google/mozc-devices/mozc-furikku/circuit.png

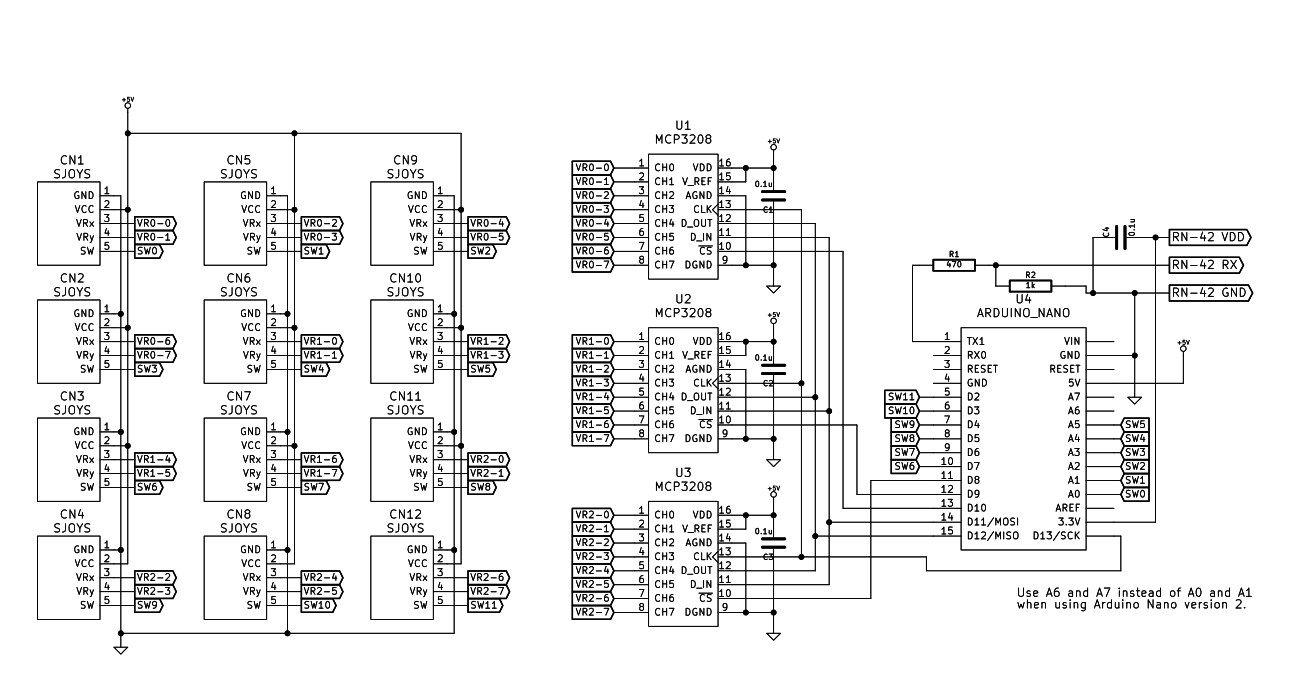
mozc-furikku/circuit.png
