google/mozc-devices/mozc-furikku/photo/device.jpg

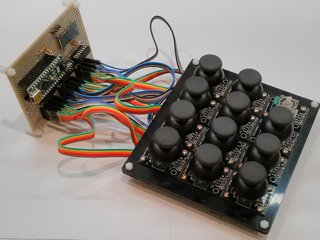
mozc-furikku/photo/device.jpg
