google/mozc-devices/mozc-furikku/photo/jsmodule.jpg

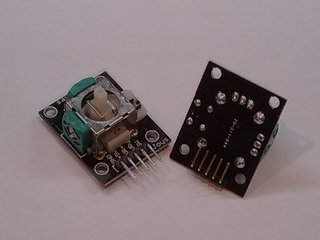
mozc-furikku/photo/jsmodule.jpg
