google/mozc-devices/mozc-furikku/photo/keyboard.jpg

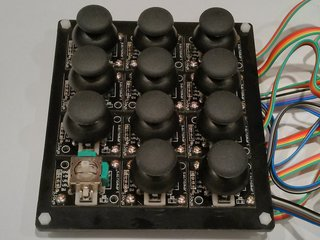
mozc-furikku/photo/keyboard.jpg
