google/mozc-devices/mozc-mageru/wireless/board/board-bottom.png

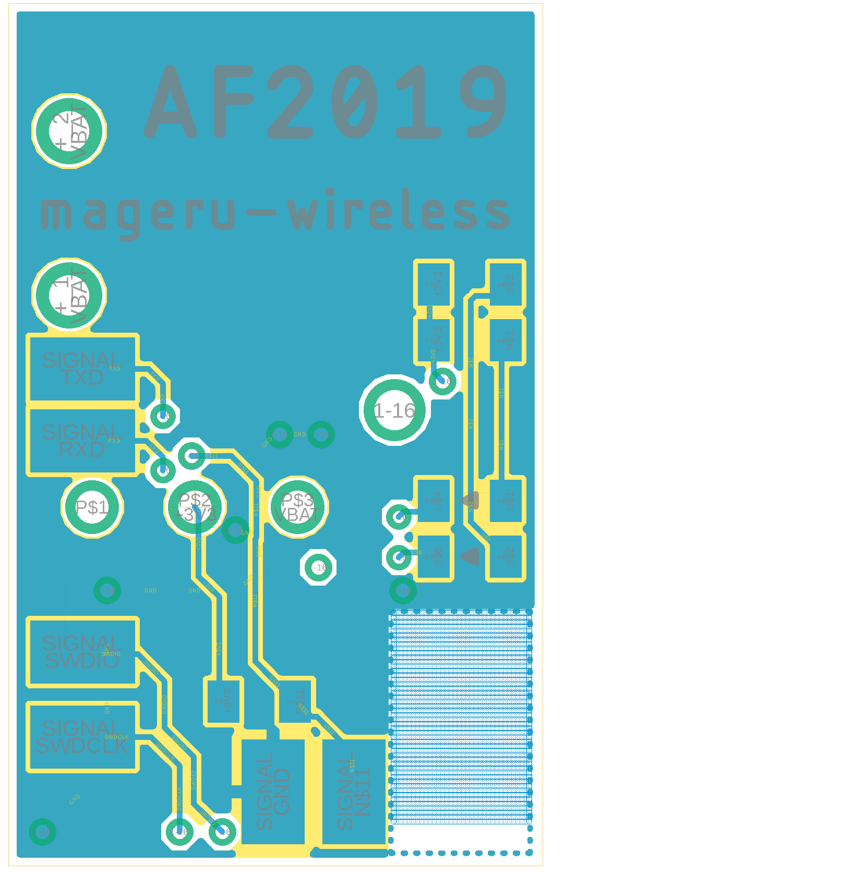
mozc-mageru/wireless/board/board-bottom.png
