google/mozc-devices/mozc-mageru/wireless/board/board-top.png

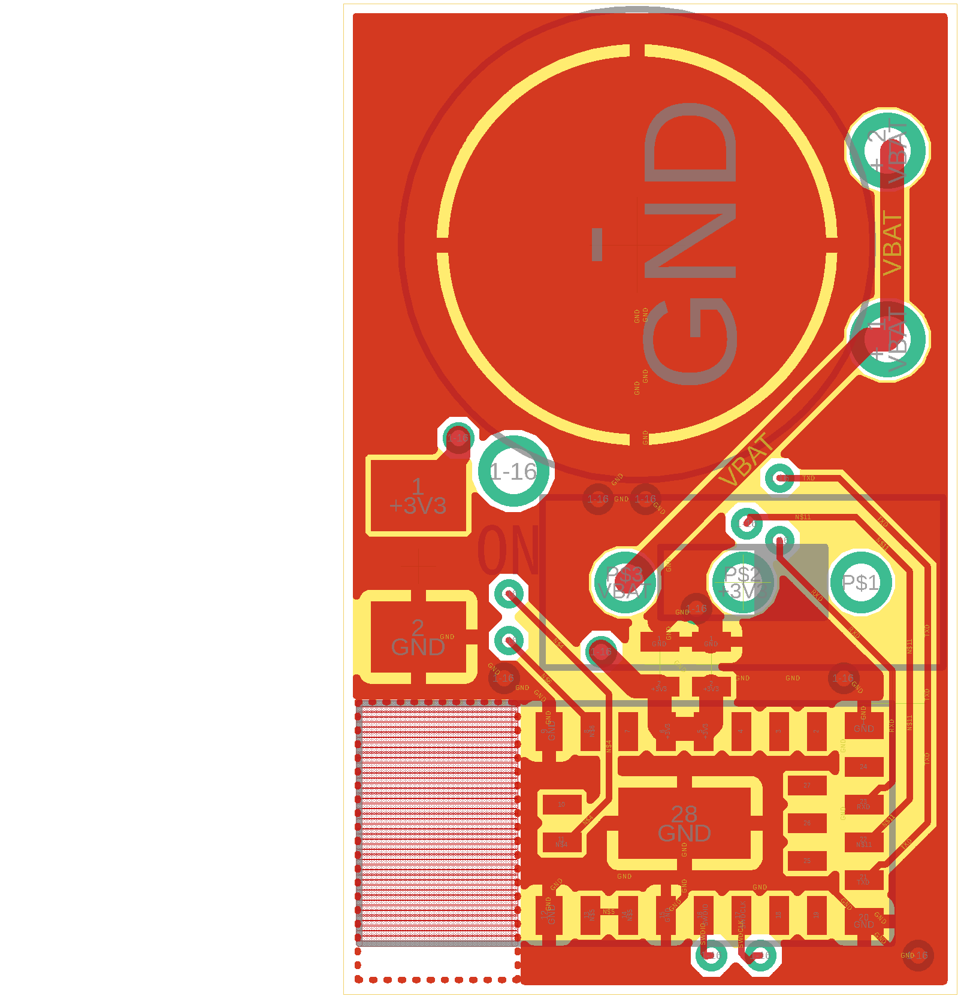
mozc-mageru/wireless/board/board-top.png
