google/mozc-devices/mozc-piropiro/circuit.png

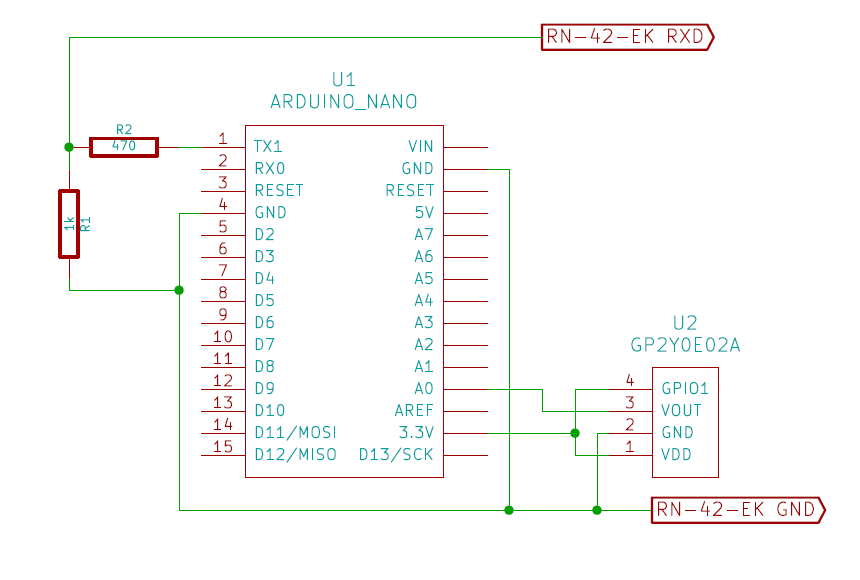
mozc-piropiro/circuit.png
