google/mozc-devices/mozc-piropiro/example.jpg

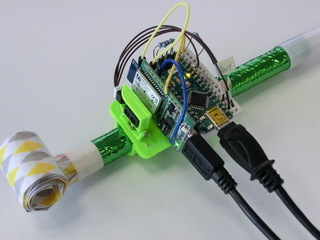
mozc-piropiro/example.jpg
