google/mozc-devices/mozc-conveyorbelt/stls/BaseCoverR.stl

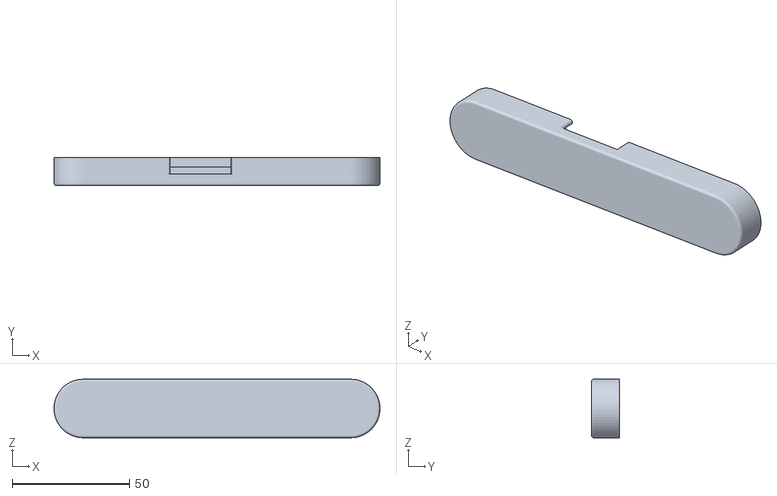
[picture p85: CAD file, 2026-10-01]
mozc-conveyorbelt/stls/BaseCoverR.stl
139.0 x 12.0 x 25.0
