google/mozc-devices/mozc-doublesided/case/case15.stl

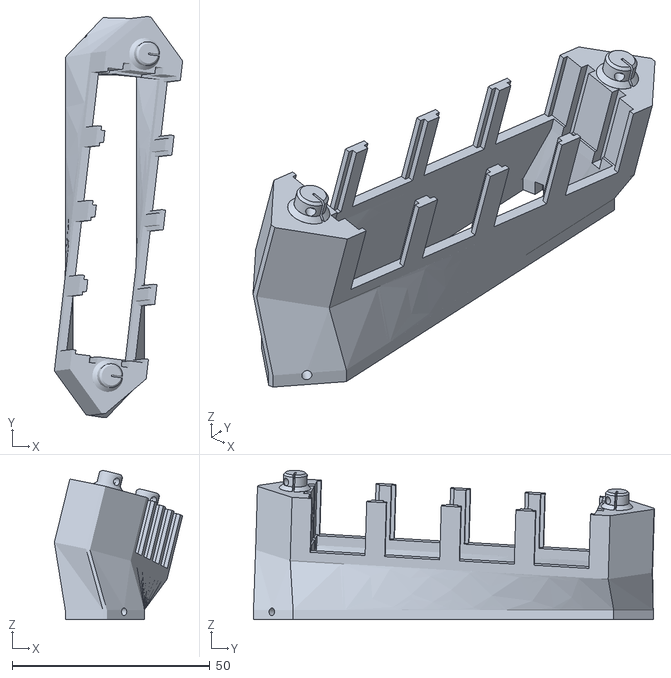
[picture p86: CAD file, 2024-10-08]
mozc-doublesided/case/case15.stl
32.4 x 101.3 x 37.7
