google/mozc-devices/mozc-piropiro/stl/arm.stl

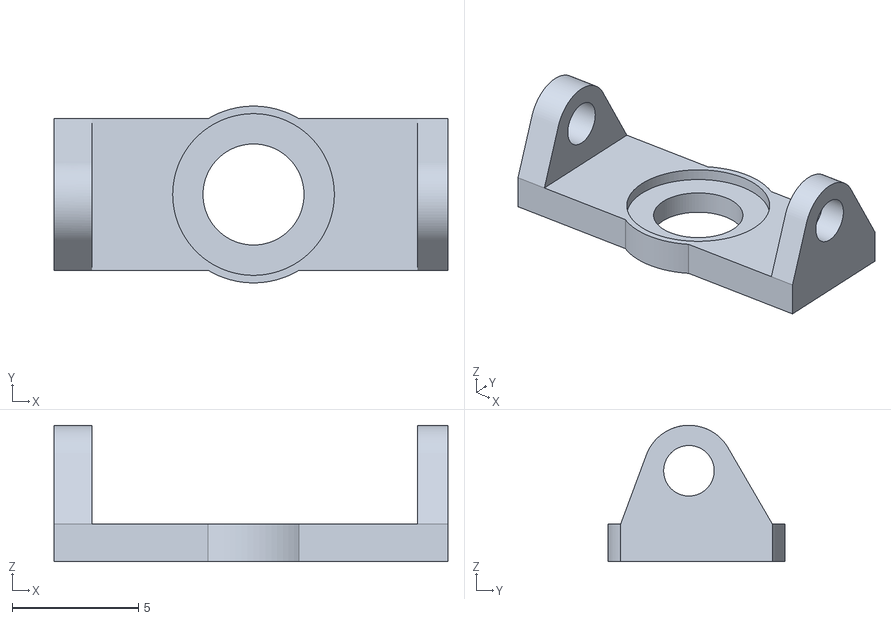
[picture p87: CAD file, 2015-08-10]
mozc-piropiro/stl/arm.stl
15.6 x 7.00 x 5.40
