google/mozc-devices/mozc-bar/case/typeE.stl

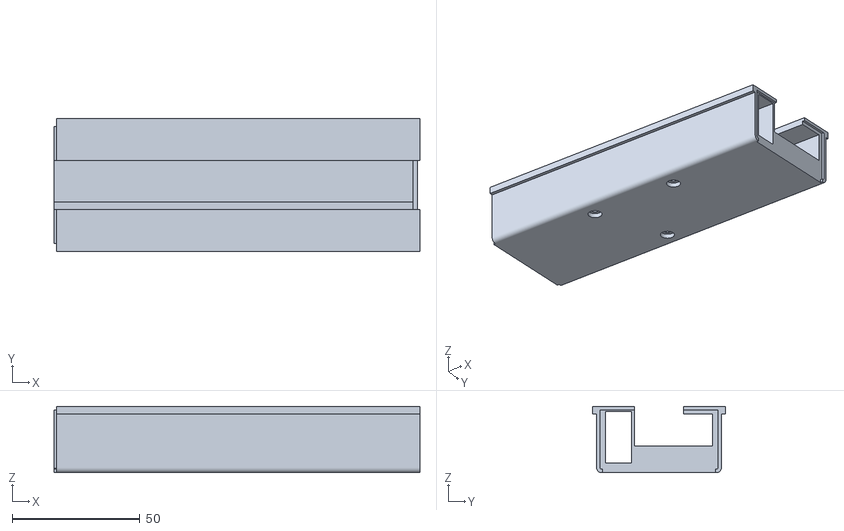
[picture p88: CAD file, 2022-10-01]
mozc-bar/case/typeE.stl
143.5 x 52.0 x 26.0
