google/mozc-devices/mozc-caps/hardware/top_plate_angle_bracket_mount.stl

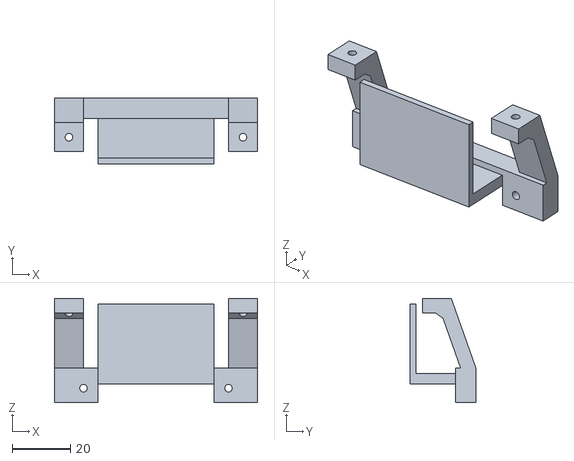
[picture p89: CAD file, 2023-10-01]
mozc-caps/hardware/top_plate_angle_bracket_mount.stl
70.0 x 22.7 x 36.0
