google/mozc-devices/mozc-conveyorbelt/stls/Cover_Top.stl

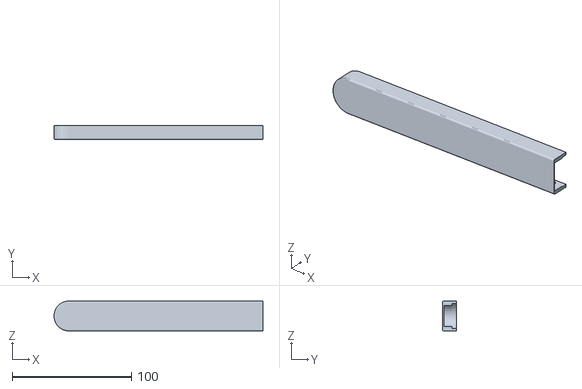
[picture p90: CAD file, 2026-10-01]
mozc-conveyorbelt/stls/Cover_Top.stl
175.0 x 12.0 x 25.0
