google/mozc-devices/mozc-doublesided/case/case03.stl

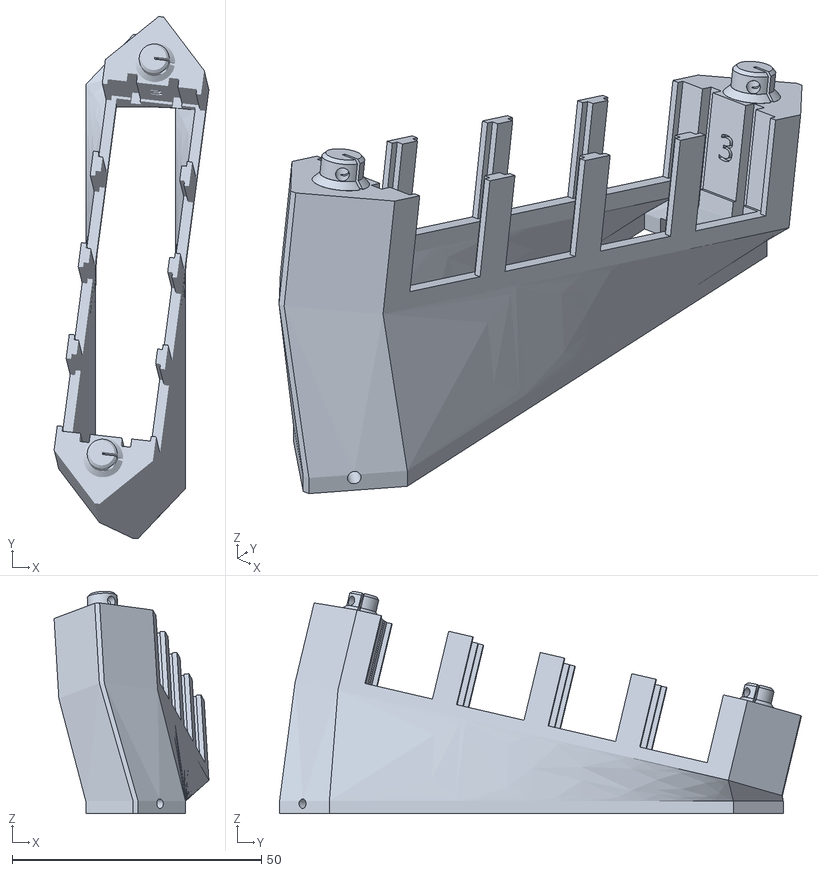
[picture p91: CAD file, 2024-10-08]
mozc-doublesided/case/case03.stl
31.0 x 104.6 x 44.6
