google/mozc-devices/mozc-bar/case/left-tip.stl

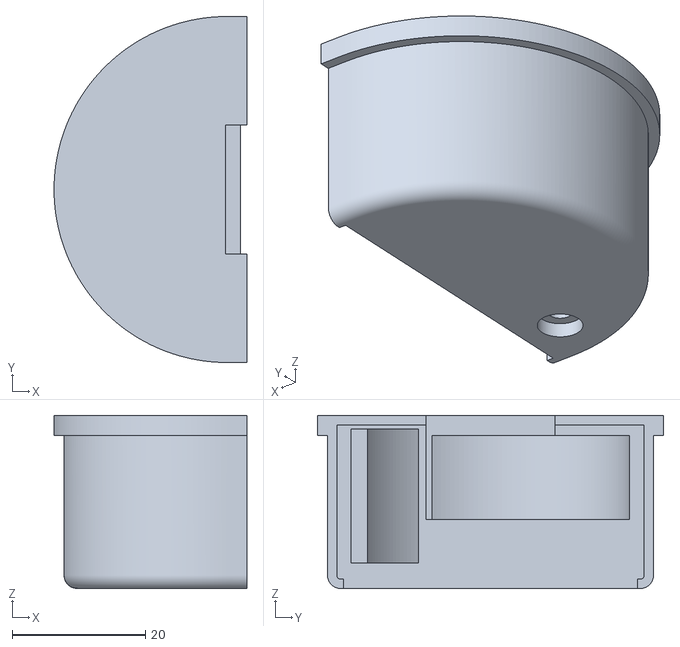
[picture p92: CAD file, 2022-10-01]
mozc-bar/case/left-tip.stl
29.0 x 52.0 x 26.0
