google/mozc-devices/mozc-caps/hardware/bump_cap_insert_mount.stl

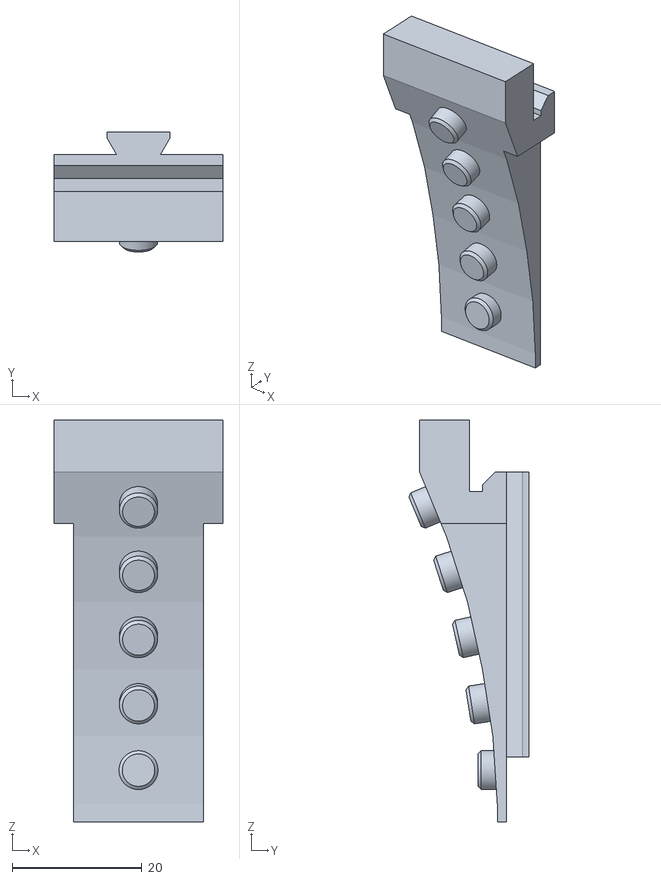
[picture p93: CAD file, 2023-10-01]
mozc-caps/hardware/bump_cap_insert_mount.stl
26.0 x 18.5 x 62.0
