google/mozc-devices/mozc-doublesided/case/case20.stl

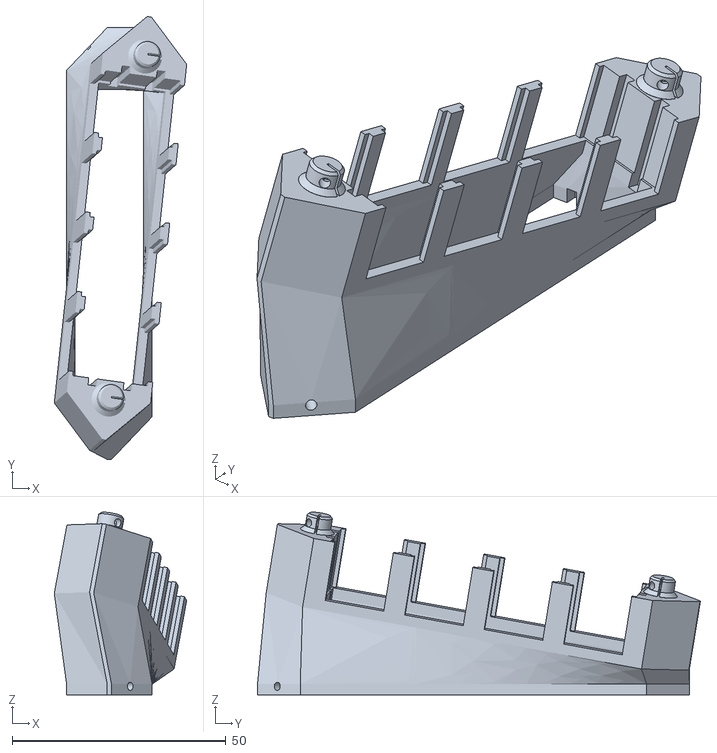
[picture p94: CAD file, 2024-10-08]
mozc-doublesided/case/case20.stl
31.0 x 103.6 x 42.7
