google/mozc-devices/mozc-piropiro/stl/base.stl

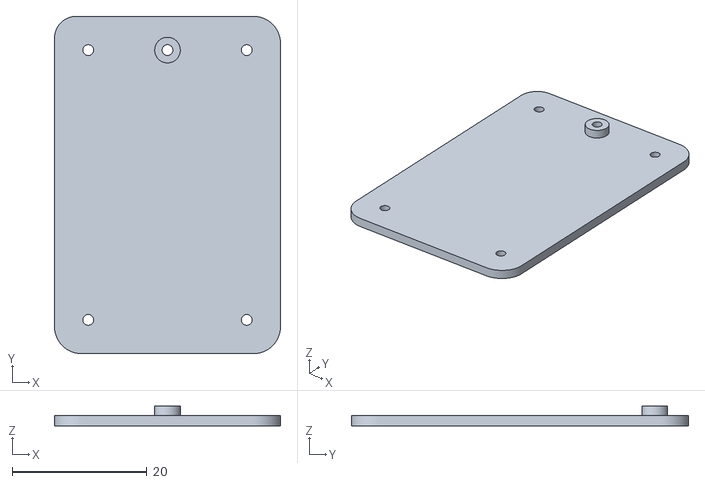
[picture p95: CAD file, 2015-08-10]
mozc-piropiro/stl/base.stl
33.5 x 50.0 x 2.90
