google/mozc-devices/mozc-bar/case/typeC.stl

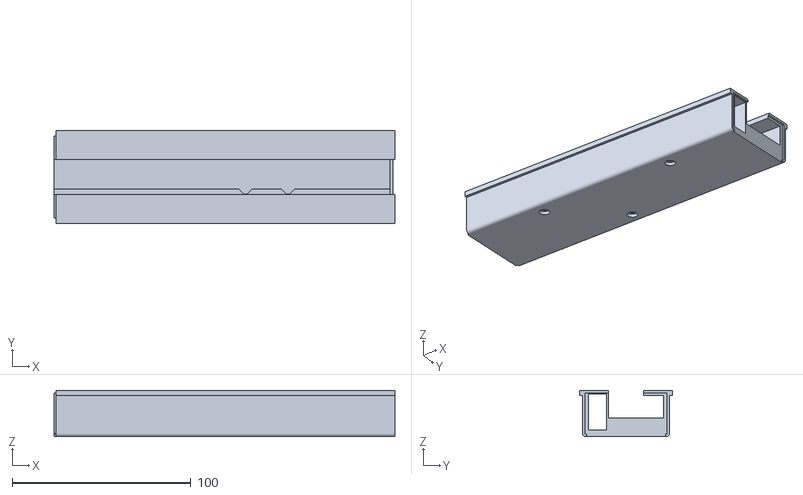
[picture p96: CAD file, 2022-10-01]
mozc-bar/case/typeC.stl
191.0 x 52.0 x 26.0
