google/mozc-devices/mozc-conveyorbelt/stls/Stay.stl

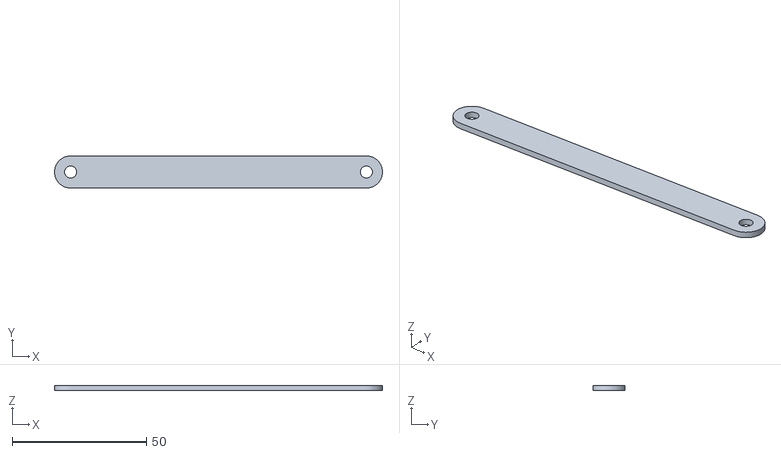
[picture p97: CAD file, 2026-10-01]
mozc-conveyorbelt/stls/Stay.stl
122.0 x 12.0 x 2.00
