google/mozc-devices/mozc-doublesided/case/case17.stl

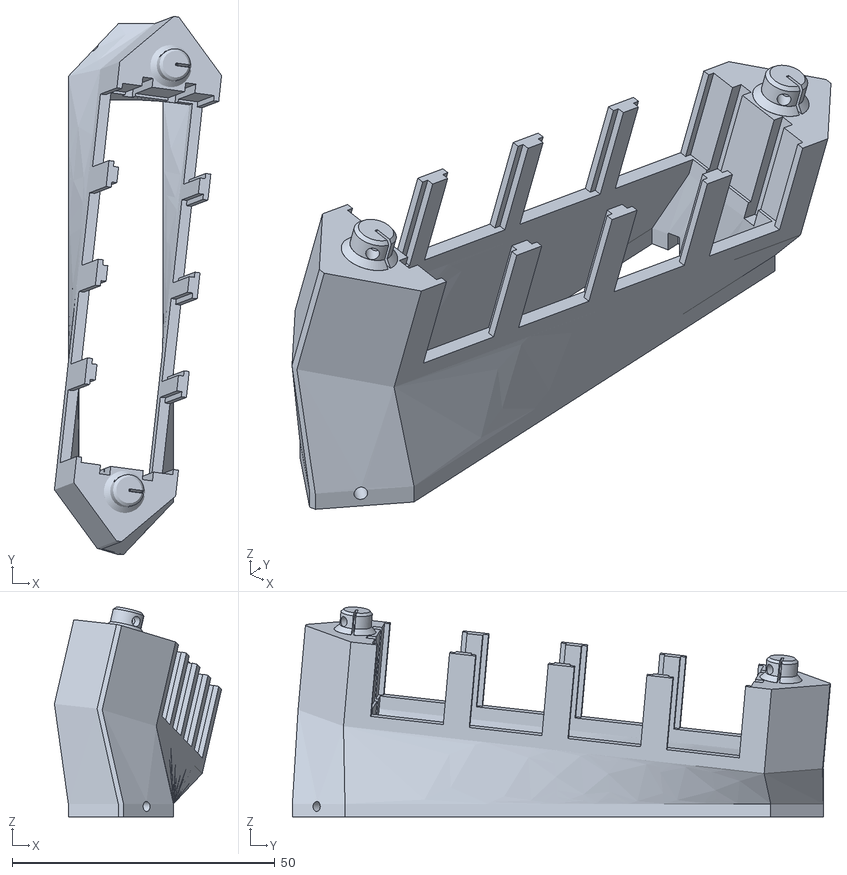
[picture p98: CAD file, 2024-10-08]
mozc-doublesided/case/case17.stl
31.8 x 102.4 x 39.9
