google/mozc-devices/mozc-bar/case/right-tip.stl

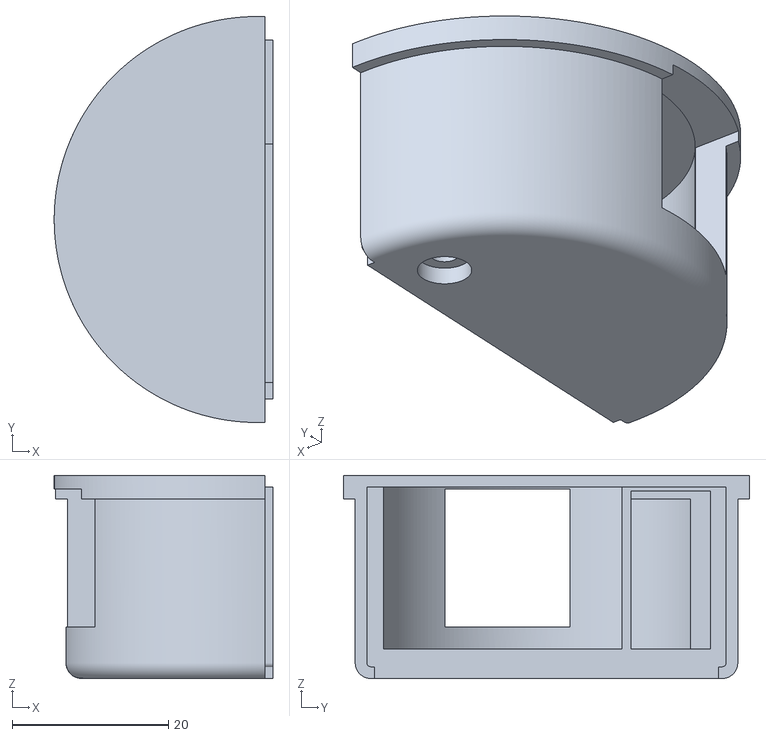
[picture p99: CAD file, 2022-10-01]
mozc-bar/case/right-tip.stl
28.0 x 52.0 x 26.0
