google/mozc-devices/mozc-conveyorbelt/stls/Box.stl

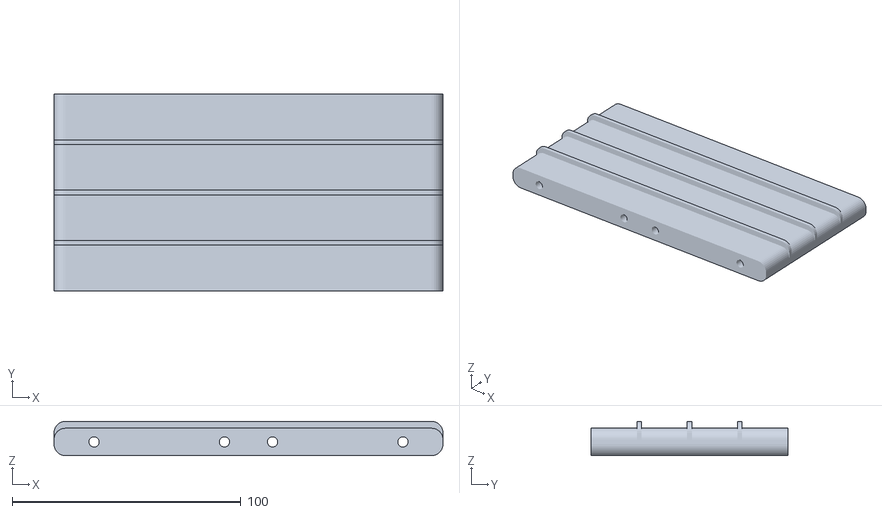
[picture p100: CAD file, 2026-10-01]
mozc-conveyorbelt/stls/Box.stl
170.0 x 86.0 x 15.0
