google/mozc-devices/mozc-doublesided/case/case08.stl

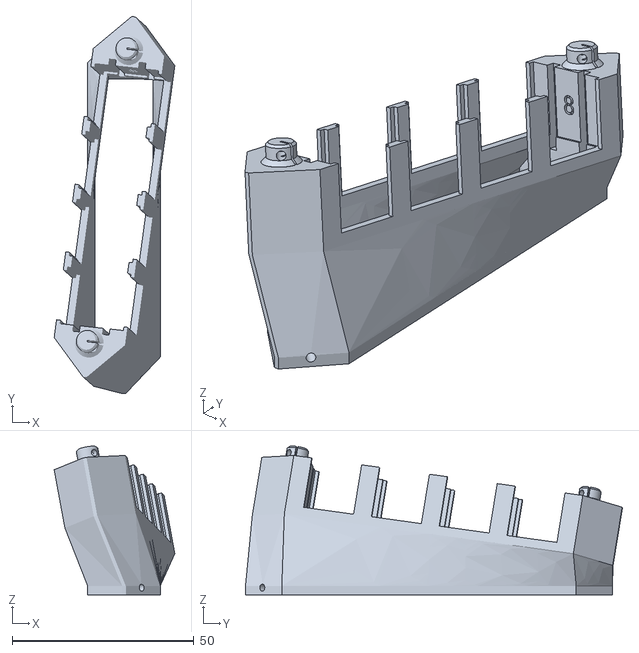
[picture p101: CAD file, 2024-10-08]
mozc-doublesided/case/case08.stl
33.2 x 103.7 x 41.0
