google/mozc-devices/mozc-bar/case/typeG.stl

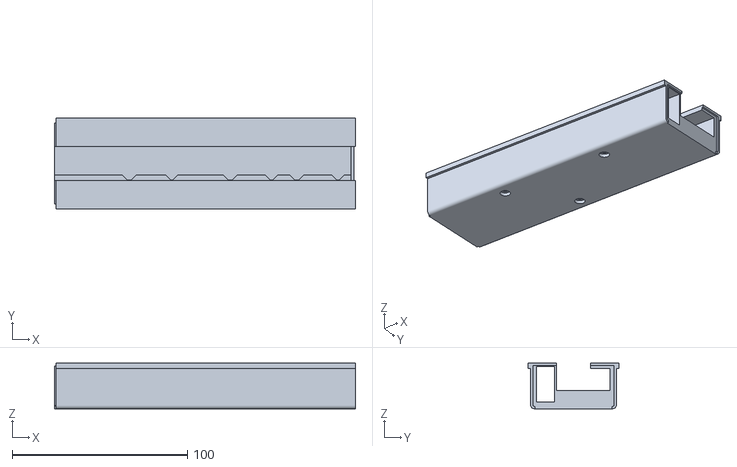
[picture p102: CAD file, 2022-10-01]
mozc-bar/case/typeG.stl
172.0 x 52.0 x 26.0
