google/mozc-devices/mozc-conveyorbelt/stls/Base_Roller.stl

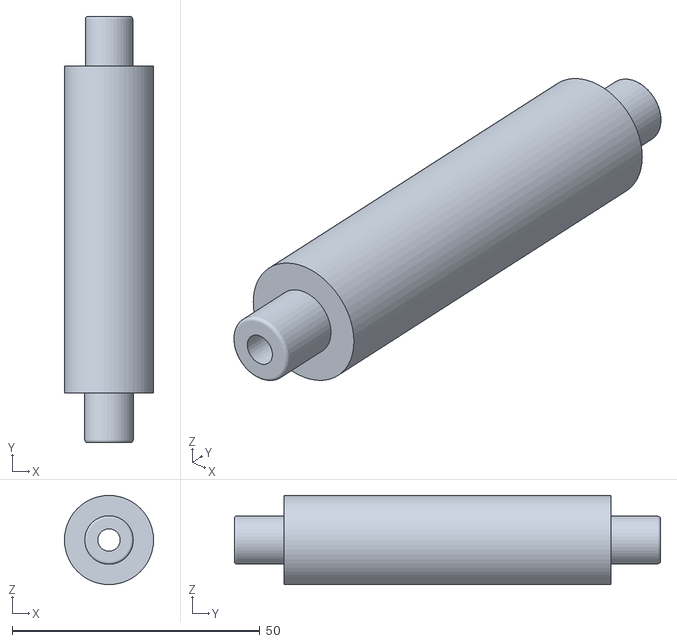
[picture p103: CAD file, 2026-10-01]
mozc-conveyorbelt/stls/Base_Roller.stl
18.0 x 86.0 x 18.0
