google/mozc-devices/mozc-bar/case/typeB.stl

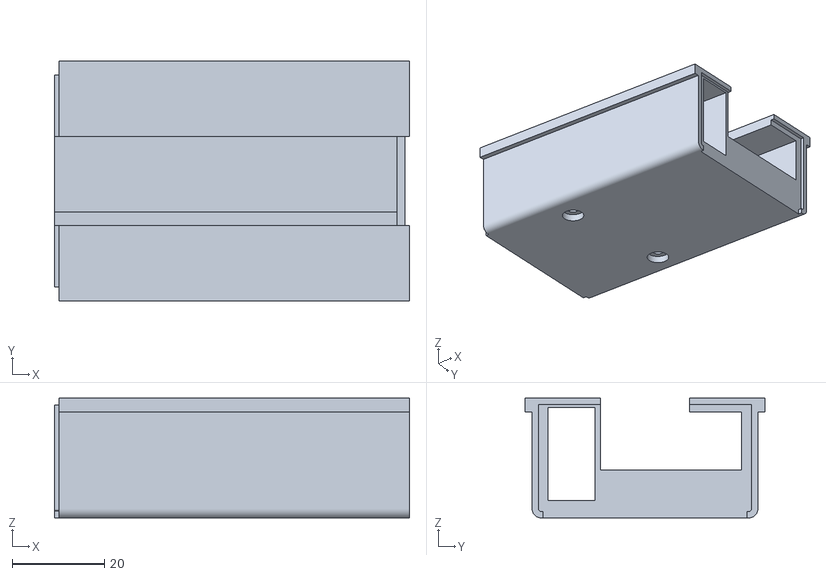
[picture p104: CAD file, 2022-10-01]
mozc-bar/case/typeB.stl
77.0 x 52.0 x 26.0
