google/mozc-devices/mozc-doublesided/case/jig.stl

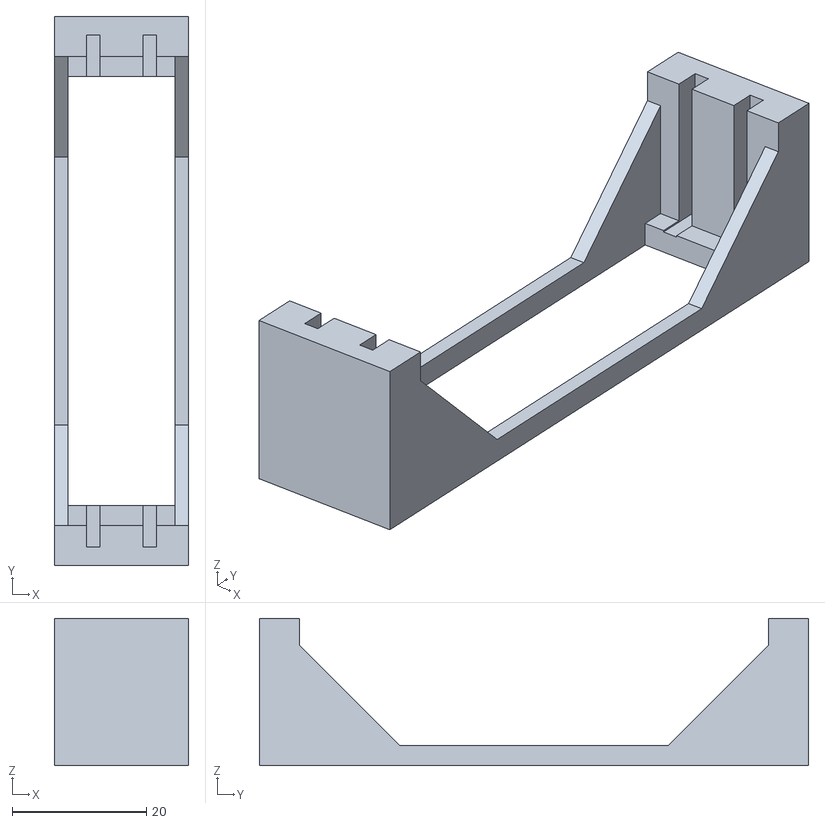
[picture p105: CAD file, 2024-10-08]
mozc-doublesided/case/jig.stl
20.0 x 82.0 x 22.0
