google/mozc-devices/mozc-bar/case/controller.stl

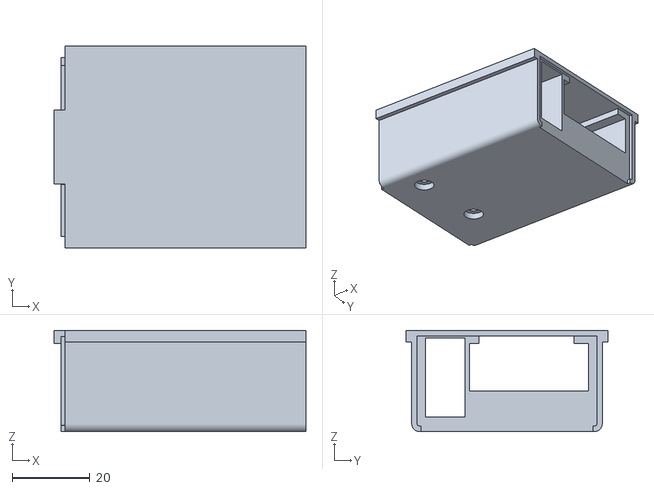
[picture p106: CAD file, 2022-10-01]
mozc-bar/case/controller.stl
64.8 x 52.0 x 26.0
