google/mozc-devices/mozc-conveyorbelt/stls/MotorSupport.stl

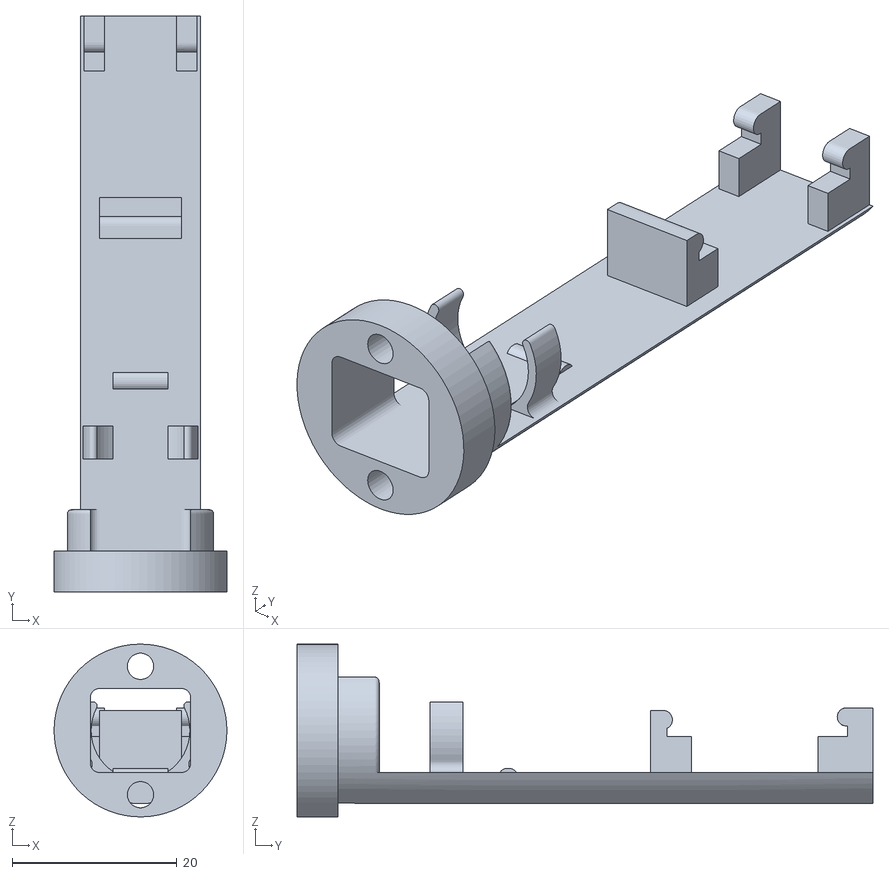
[picture p107: CAD file, 2026-10-01]
mozc-conveyorbelt/stls/MotorSupport.stl
21.0 x 70.0 x 21.0
