google/mozc-devices/mozc-doublesided/case/case16.stl

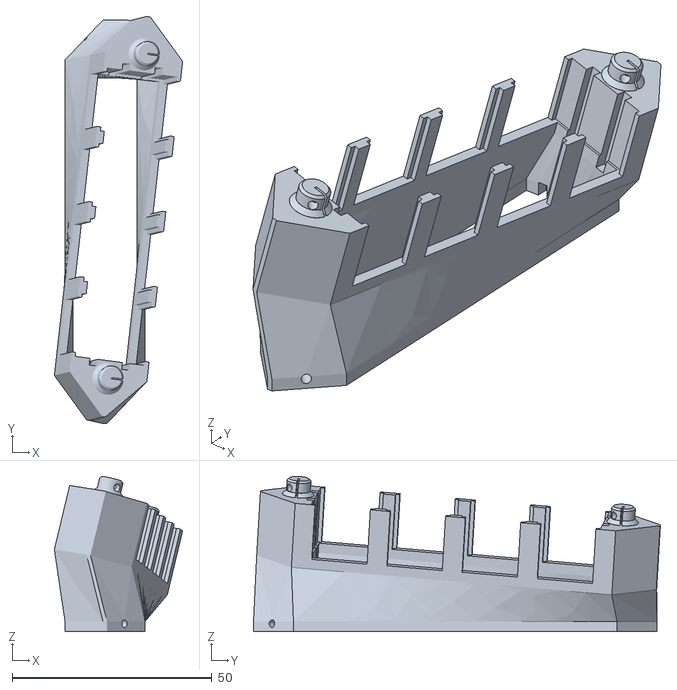
[picture p108: CAD file, 2024-10-08]
mozc-doublesided/case/case16.stl
32.1 x 101.9 x 38.9
