google/mozc-devices/mozc-conveyorbelt/stls/Belt.stl

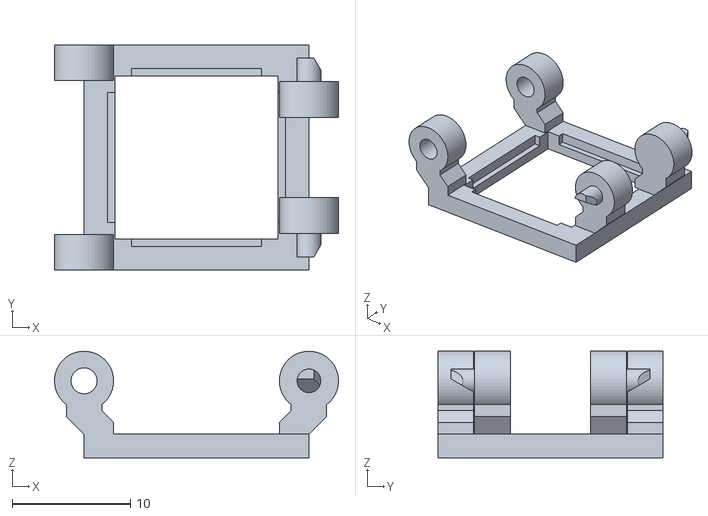
[picture p109: CAD file, 2026-10-01]
mozc-conveyorbelt/stls/Belt.stl
24.0 x 19.0 x 9.00
