google/mozc-devices/mozc-doublesided/case/case13.stl

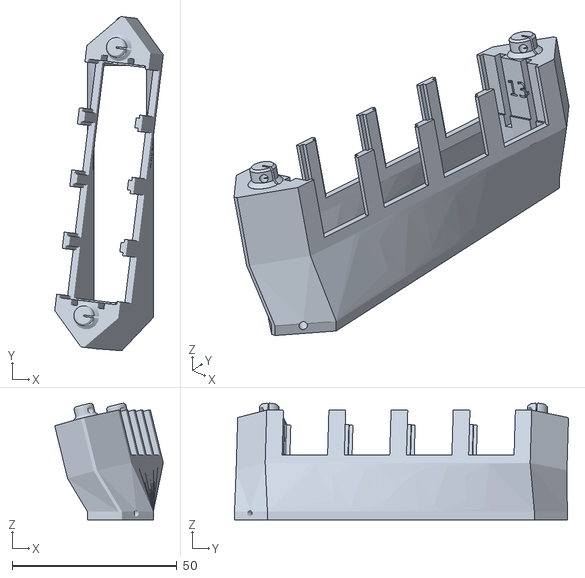
[picture p110: CAD file, 2024-10-08]
mozc-doublesided/case/case13.stl
33.0 x 101.3 x 35.4
