google/mozc-devices/mozc-conveyorbelt/stls/BottomTubePlate.stl

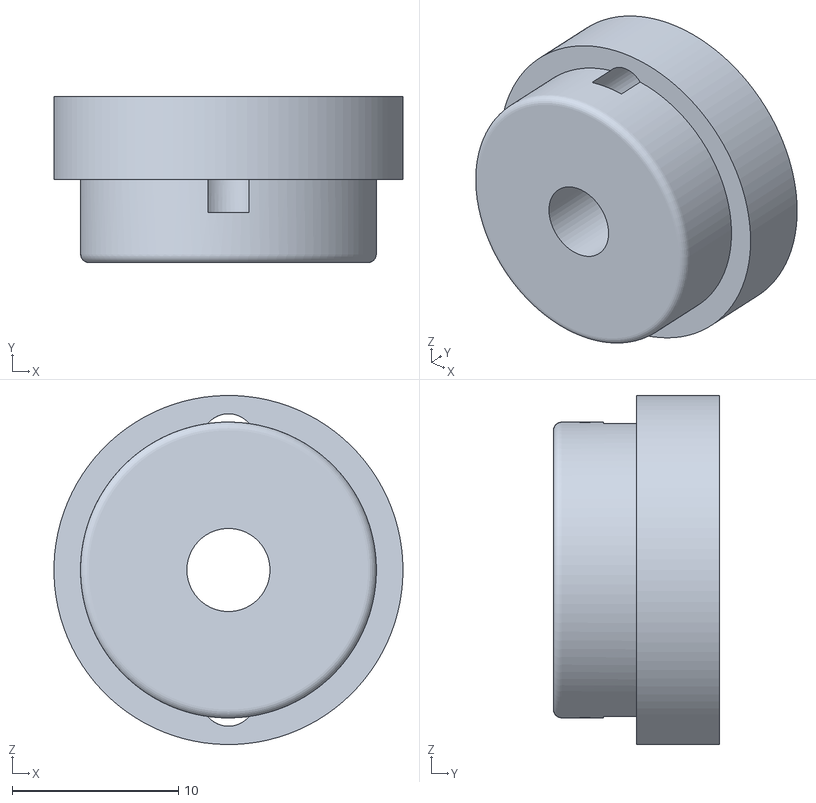
[picture p111: CAD file, 2026-10-01]
mozc-conveyorbelt/stls/BottomTubePlate.stl
21.0 x 10.0 x 21.0
