google/mozc-devices/mozc-doublesided/case/case10.stl

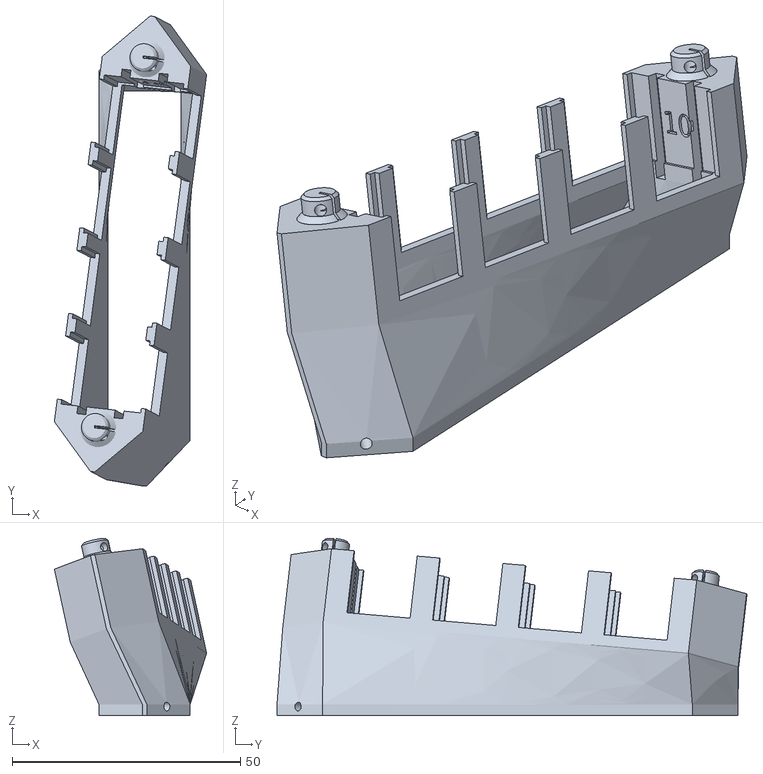
[picture p112: CAD file, 2024-10-08]
mozc-doublesided/case/case10.stl
33.4 x 103.0 x 38.9
