google/mozc-devices/mozc-conveyorbelt/stls/SprocketA.stl

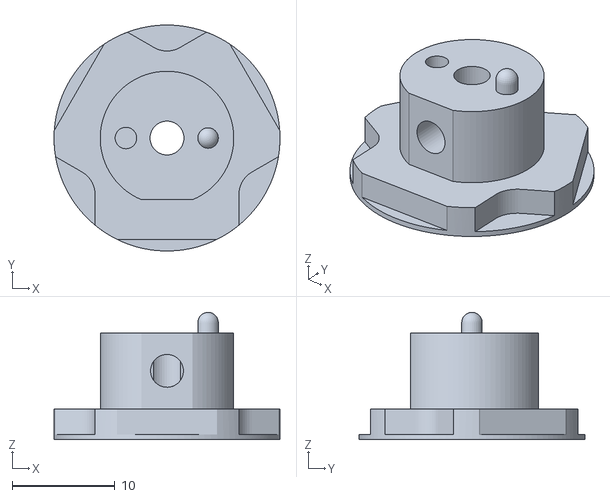
[picture p113: CAD file, 2026-10-01]
mozc-conveyorbelt/stls/SprocketA.stl
22.0 x 22.0 x 12.4
