google/mozc-devices/mozc-doublesided/case/case06.stl

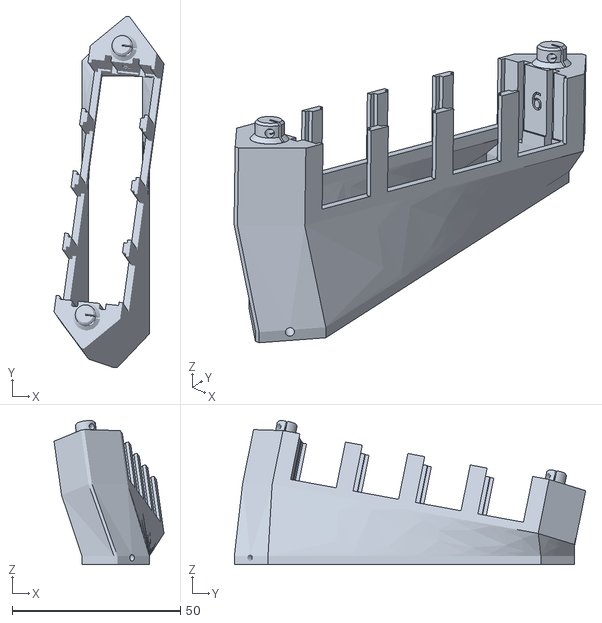
[picture p114: CAD file, 2024-10-08]
mozc-doublesided/case/case06.stl
32.6 x 104.3 x 42.7
