google/mozc-devices/mozc-conveyorbelt/stls/Cover_BottomL.stl

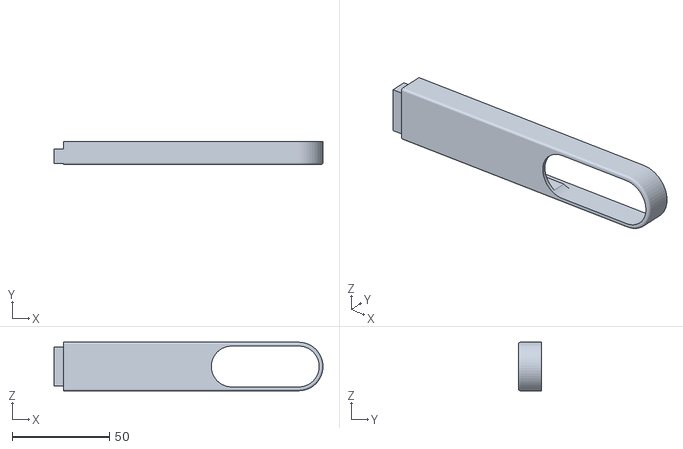
[picture p115: CAD file, 2026-10-01]
mozc-conveyorbelt/stls/Cover_BottomL.stl
138.5 x 12.0 x 25.0
