google/mozc-devices/mozc-conveyorbelt/stls/SidePlate_Top.stl

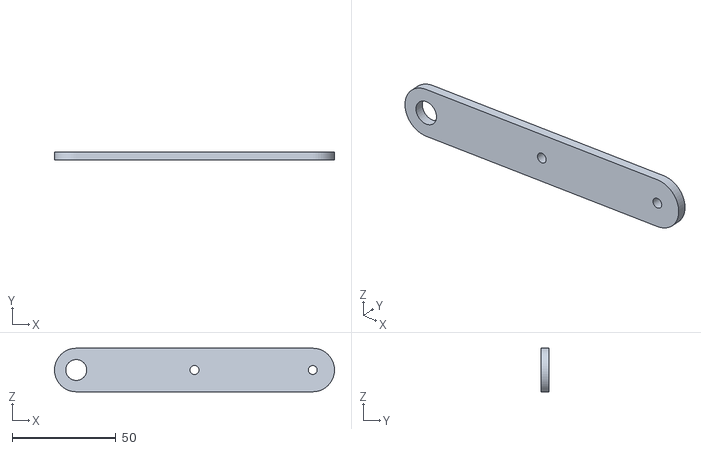
[picture p116: CAD file, 2026-10-01]
mozc-conveyorbelt/stls/SidePlate_Top.stl
135.0 x 4.00 x 21.0
