google/mozc-devices/mozc-doublesided/case/case11.stl

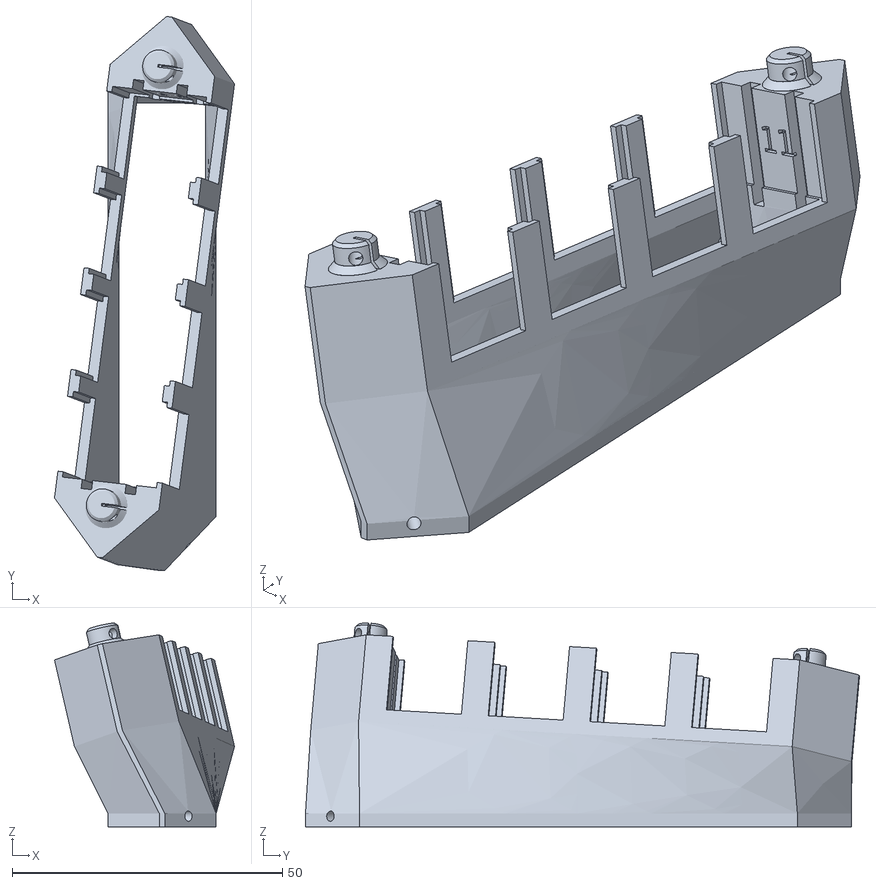
[picture p117: CAD file, 2024-10-08]
mozc-doublesided/case/case11.stl
33.3 x 102.5 x 37.7
