google/mozc-devices/mozc-conveyorbelt/stls/Base_Side.stl

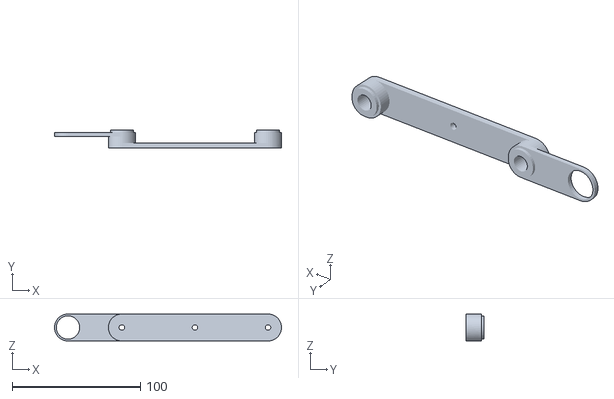
[picture p118: CAD file, 2026-10-01]
mozc-conveyorbelt/stls/Base_Side.stl
177.0 x 14.0 x 21.0
