google/mozc-devices/mozc-doublesided/case/case22.stl

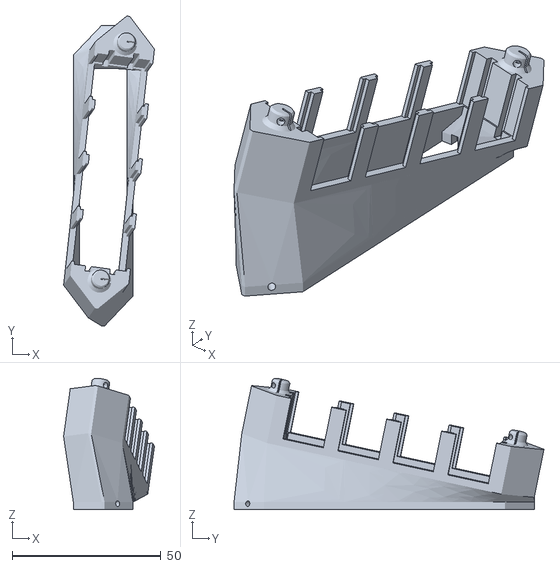
[picture p119: CAD file, 2024-10-08]
mozc-doublesided/case/case22.stl
30.5 x 104.1 x 44.1
