google/mozc-devices/mozc-conveyorbelt/stls/SidePlate_Bottom.stl

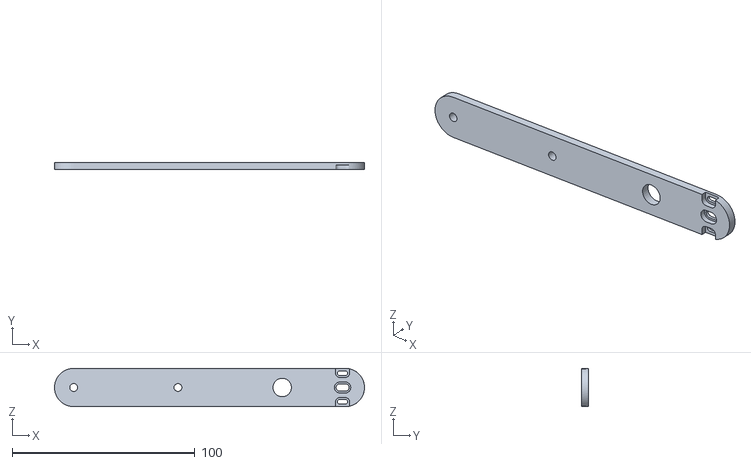
[picture p120: CAD file, 2026-10-01]
mozc-conveyorbelt/stls/SidePlate_Bottom.stl
169.5 x 4.00 x 21.0
