google/mozc-devices/mozc-doublesided/case/case25.stl

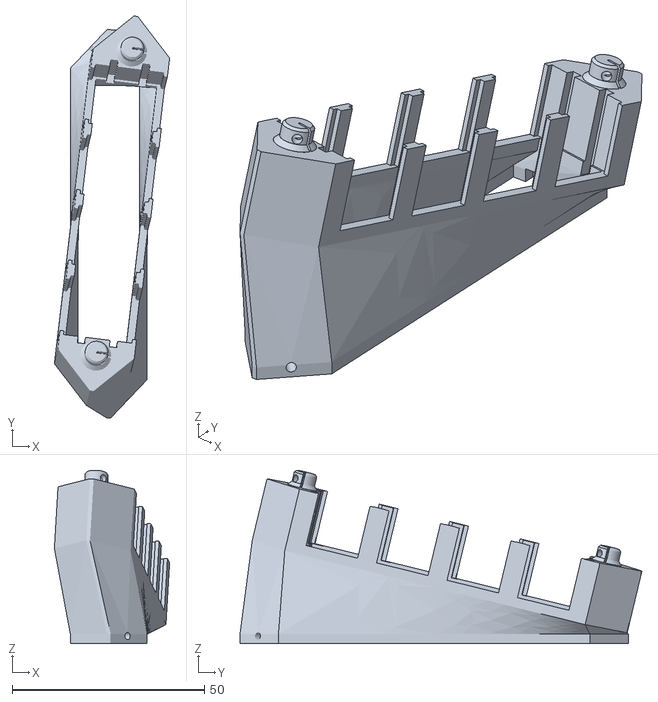
[picture p121: CAD file, 2024-10-08]
mozc-doublesided/case/case25.stl
30.0 x 104.6 x 45.1
