google/mozc-devices/mozc-doublesided/case/case04.stl

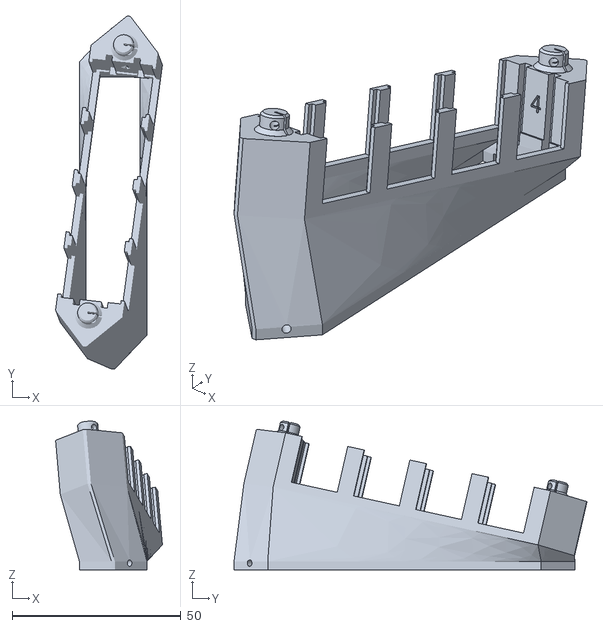
[picture p122: CAD file, 2024-10-08]
mozc-doublesided/case/case04.stl
31.7 x 104.6 x 44.1
