google/mozc-devices/mozc-doublesided/case/case05.stl

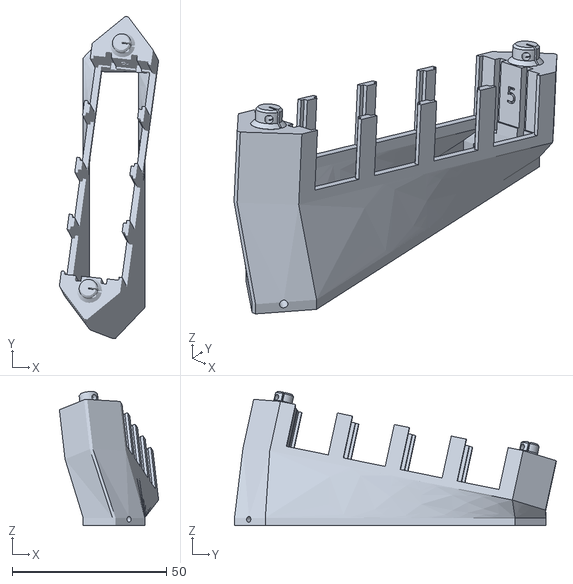
[picture p123: CAD file, 2024-10-08]
mozc-doublesided/case/case05.stl
32.2 x 104.4 x 43.5
