google/mozc-devices/mozc-doublesided/case/case19.stl

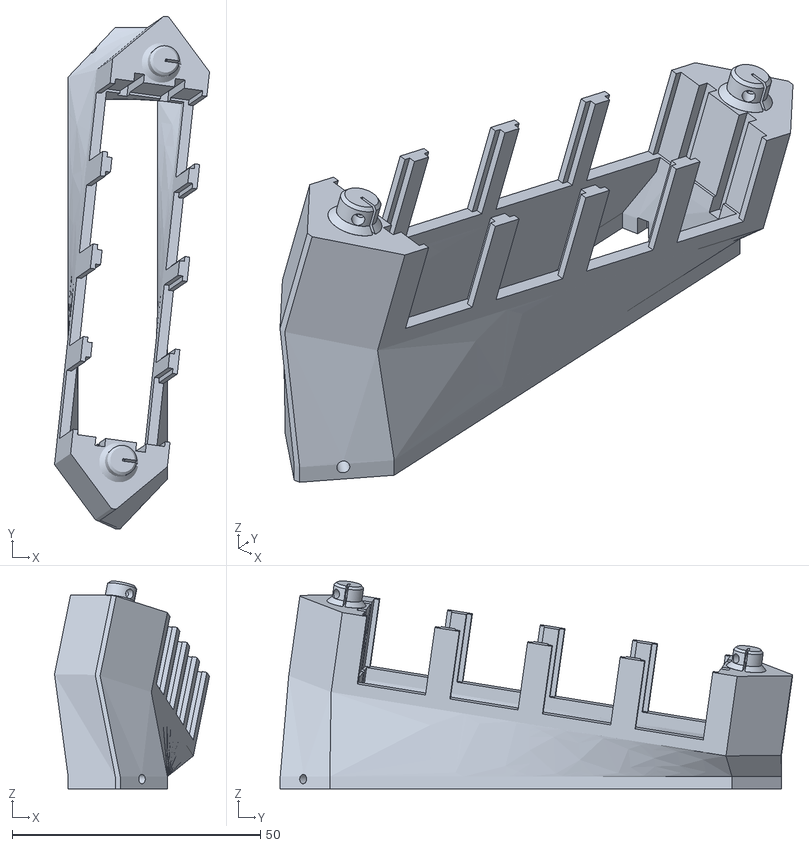
[picture p124: CAD file, 2024-10-08]
mozc-doublesided/case/case19.stl
31.2 x 103.2 x 41.9
