google/mozc-devices/mozc-doublesided/case/case00.stl

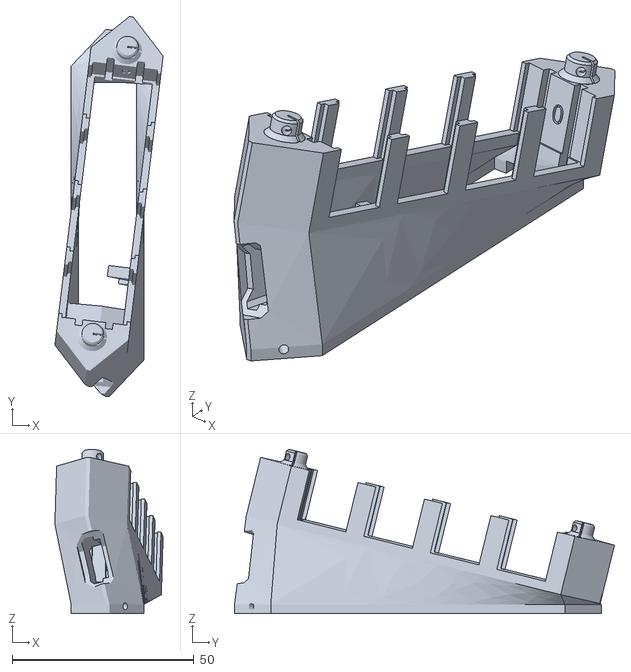
[picture p125: CAD file, 2024-10-08]
mozc-doublesided/case/case00.stl
29.8 x 104.6 x 45.2
