google/mozc-devices/mozc-doublesided/case/case07.stl

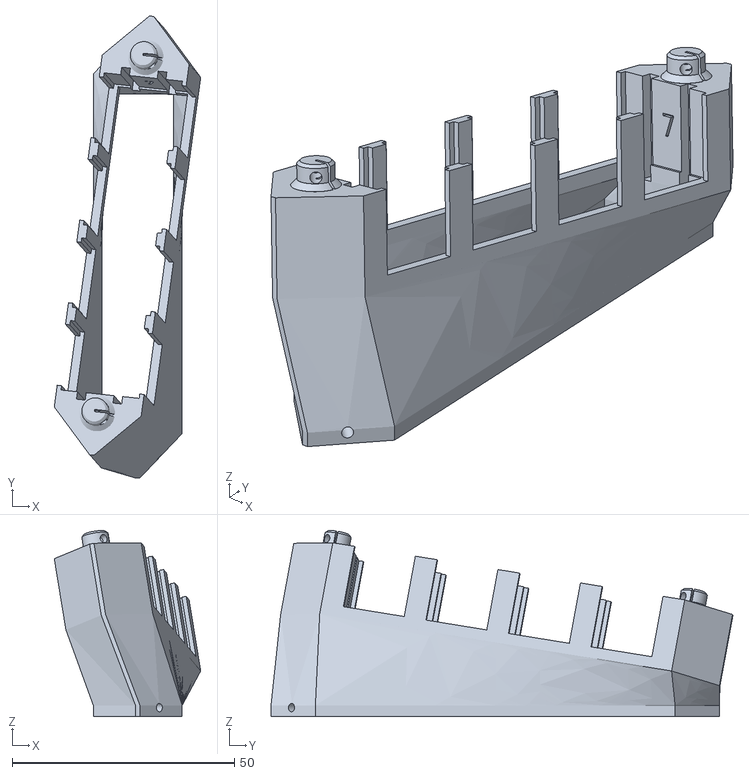
[picture p126: CAD file, 2024-10-08]
mozc-doublesided/case/case07.stl
33.0 x 104.0 x 41.9
