google/mozc-devices/mozc-doublesided/case/case09.stl

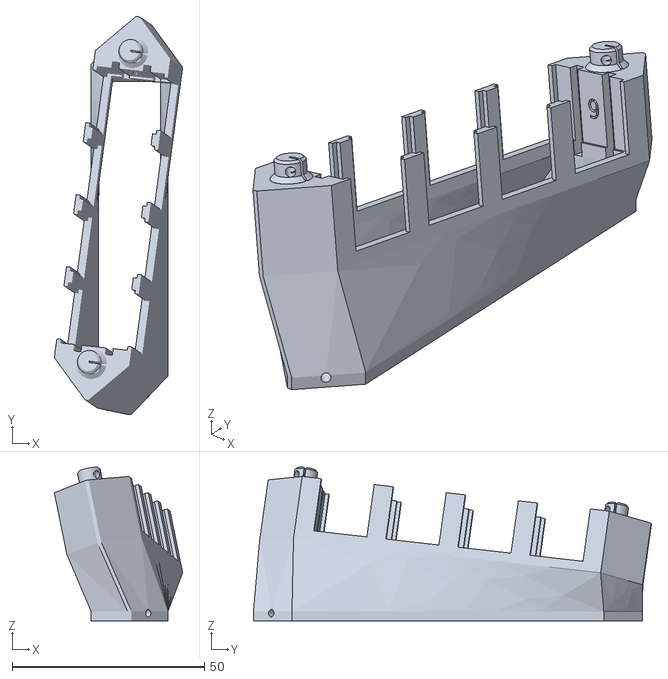
[picture p127: CAD file, 2024-10-08]
mozc-doublesided/case/case09.stl
33.3 x 103.4 x 39.9
