google/mozc-devices/mozc-yunomi/board/base-promicro/base-promicro.kicad_pcb

## KiCad design mozc-yunomi/board/base-promicro/base-promicro.kicad_pcb (2021-12-22)

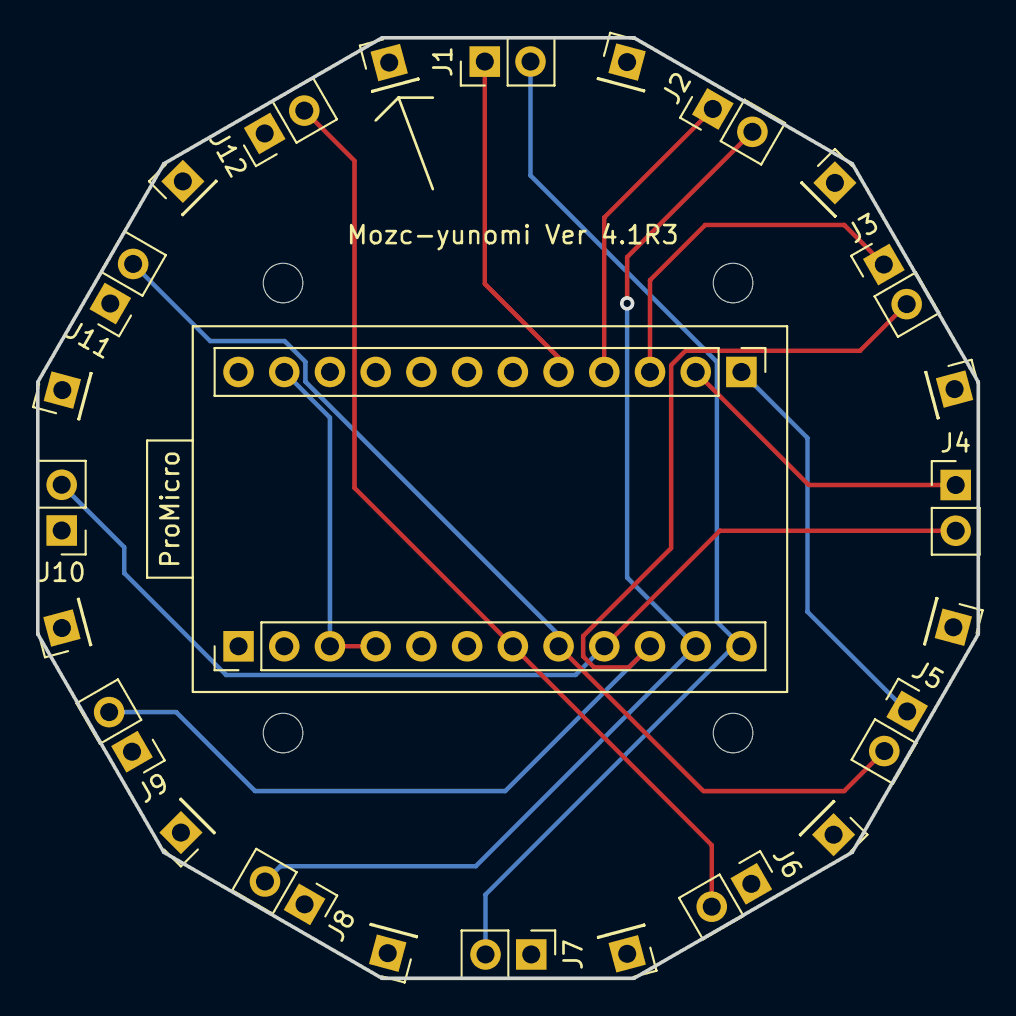
[picture p141: board base-promicro.kicad_pcb from above]

Board: 2 copper layers, 52.2 x 52.2 mm, 30 parts (0 on the bottom side), 12 nets.

Parts:
H1, H2, H3, H4: MountingHole; MountingHole_2.2mm_M2
J1, J2, J3, J4, J5, J6, J7, J8, J9, J10, J11, J12: Conn_01x02_Male; PinHeader_1x02_P2.54mm_Vertical
J13, J14: Conn_01x12; PinHeader_1x12_P2.54mm_Vertical
J15, J16, J17, J18, J19, J20, J21, J22, J23, J24, J25, J26: Conn_01x01_Male; PinHeader_1x01_P2.54mm_Vertical

Connections:
COL0: J1.2, J7.2, J13.12
COL1: J2.2, J8.2, J13.11
COL2: J3.2, J9.2, J13.10
COL3: J4.2, J10.2, J13.9
COL4: J5.2, J11.2, J13.8
COL5: J6.2, J12.2, J13.7
GND: J13.3, J13.4, J14.11
ROW0: J1.1, J14.5
ROW1: J2.1, J14.4
ROW2: J3.1, J14.3
ROW3: J4.1, J14.2
ROW4: J5.1, J14.1
