google/mozc-devices/mozc-yunomi/board/base/base.kicad_pcb

## KiCad design mozc-yunomi/board/base/base.kicad_pcb (2021-10-08)

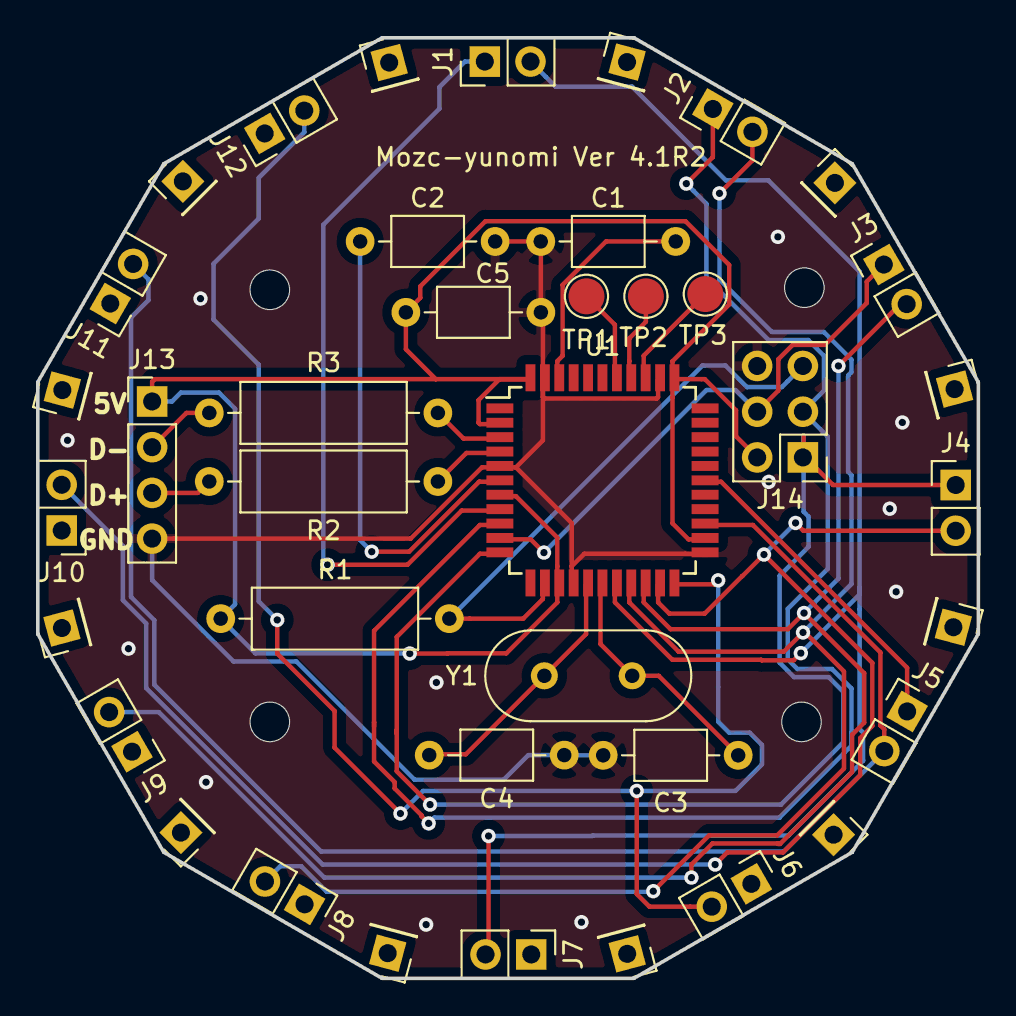
[picture p142: board base.kicad_pcb from above]

Board: 2 copper layers, 52.2 x 52.2 mm, 39 parts (0 on the bottom side), 25 nets.

Parts:
C1: 0.1uF; C_Axial_L3.8mm_D2.6mm_P7.50mm_Horizontal
C2: 1uF; C_Axial_L3.8mm_D2.6mm_P7.50mm_Horizontal
C3, C4, C5: C; C_Axial_L3.8mm_D2.6mm_P7.50mm_Horizontal
J1, J2, J3, J4, J5, J6, J7, J8, J9, J10, J11, J12: Conn_01x02_Male; PinHeader_1x02_P2.54mm_Vertical
J13: Conn_01x04_Male; PinHeader_1x04_P2.54mm_Vertical
J14: Conn_02x03_Odd_Even; PinHeader_2x03_P2.54mm_Vertical
J15, J16, J17, J18, J19, J20, J21, J22, J23, J24, J25, J26: Conn_01x01_Male; PinHeader_1x01_P2.54mm_Vertical
R1: 10K; R_Axial_DIN0309_L9.0mm_D3.2mm_P12.70mm_Horizontal
R2, R3: 22; R_Axial_DIN0309_L9.0mm_D3.2mm_P12.70mm_Horizontal
TP1, TP2, TP3: TestPoint; TestPoint_Pad_D2.0mm
U1: ATmega32U4-AU; TQFP-44_10x10mm_P0.8mm
Y1: 16MHz; Crystal_HC49-4H_Vertical

Connections:
+5V: C5.1, J13.1, J14.2, R1.1, U1.2, U1.7, U1.14, U1.24, U1.34, U1.44
COL0: J1.2, J7.2, U1.18
COL1: J2.2, J8.2, U1.19
COL2: J3.2, J9.2, U1.20
COL3: J4.2, J10.2, U1.21
COL4: J5.2, J11.2, U1.25
COL5: J6.2, J12.2, U1.22
D+: J13.3, R2.2
D-: J13.2, R3.2
GND: C1.1, C2.2, C3.1, C4.1, C5.2, J13.4, J14.6, U1.5, U1.15, U1.23, U1.35, U1.43
MISO: J4.1, J14.1, U1.11
MOSI: J3.1, J14.4, U1.10
unnamed: C1.2, U1.42
unnamed: C2.1, U1.6
unnamed: R2.1, U1.4
unnamed: R3.1, U1.3
unnamed: TP1.1, U1.38
unnamed: TP2.1, U1.37
unnamed: TP3.1, U1.36
ROW0: J1.1, U1.8
ROW1: J2.1, J14.3, U1.9
ROW4: J5.1, U1.28
RST: J14.5, R1.2, U1.13
XTAL1: C3.2, U1.17, Y1.1
XTAL2: C4.2, U1.16, Y1.2
