google/mozc-devices/mozc-yunomi/board/key/yunomi.kicad_pcb

## KiCad design mozc-yunomi/board/key/yunomi.kicad_pcb (2021-09-30)

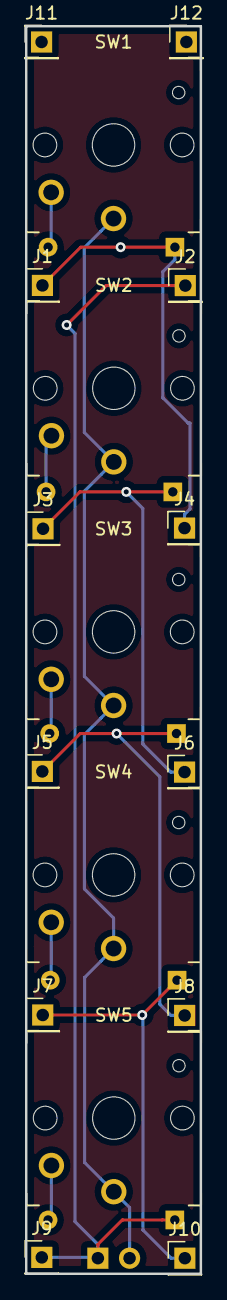
[picture p143: board yunomi.kicad_pcb from above]

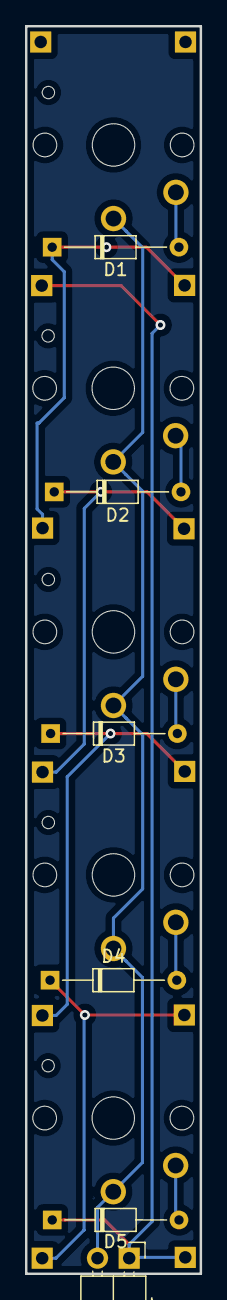
[picture p144: board yunomi.kicad_pcb from below]

Board: 2 copper layers, 14.0 x 100.0 mm, 23 parts (6 on the bottom side), 11 nets.

Parts:
D1, D2, D3, D4, D5: D; D_DO-34_SOD68_P10.16mm_Horizontal
J1, J2, J3, J4, J5, J6, J7, J8, J9, J10, J11, J12: Conn_01x01_Male; PinHeader_1x01_P2.54mm_Vertical
J13: Conn_01x02_Male; PinHeader_1x02_P2.54mm_Horizontal
SW1, SW2, SW3, SW4, SW5: SW_Push; SW_PG1350

Connections:
unnamed: D1.1, J1.1, J4.1
unnamed: D1.2, SW1.2
unnamed: D2.1, J3.1, J6.1
unnamed: D2.2, SW2.2
unnamed: D3.1, J5.1, J8.1
unnamed: D3.2, SW3.2
unnamed: D4.1, J7.1, J10.1
unnamed: D4.2, SW4.2
unnamed: D5.1, J2.1, J9.1, J13.1
unnamed: D5.2, SW5.2
unnamed: J13.2, SW1.1, SW2.1, SW3.1, SW4.1, SW5.1
