google/mozc-devices/mozc-nazoru/src/nazoru/nazorunet.py

# -*- coding: utf-8 -*-
#
# Copyright 2018 Google LLC
#
# Licensed under the Apache License, Version 2.0 (the "License");
# you may not use this file except in compliance with the License.
# You may obtain a copy of the License at
#
#      http://www.apache.org/licenses/LICENSE-2.0
#
# Unless required by applicable law or agreed to in writing, software
# distributed under the License is distributed on an "AS IS" BASIS,
# WITHOUT WARRANTIES OR CONDITIONS OF ANY KIND, either express or implied.
# See the License for the specific language governing permissions and
# limitations under the License.
"""NazoruNet.

NazoruNet is a customized version of MobileNet architecture and can be used to
predict input characters from visualized trace.
"""

from collections import namedtuple
import tf_slim as slim
import tensorflow.compat.v1 as tf

Conv = namedtuple('Conv', ['kernel', 'stride', 'depth'])
DepthSepConv = namedtuple('DepthSepConv', ['kernel', 'stride', 'depth'])


def mobilenet_v1_base(inputs,
                      final_endpoint,
                      conv_defs,
                      min_depth=8,
                      depth_multiplier=1.0,
                      bn_decay=0.95,
                      output_stride=None,
                      scope=None):
  """Mobilenet v1.
  Constructs a Mobilenet v1 network from inputs to the given final endpoint.
  Customized to accept batch normalization decay parameter to accelerate
  learning speed.
  Args:
    inputs: a tensor of shape [batch_size, height, width, channels].
    final_endpoint: specifies the endpoint to construct the network up to. It
      can be one of ['Conv2d_0', 'Conv2d_1_pointwise', 'Conv2d_2_pointwise',
      'Conv2d_3_pointwise', 'Conv2d_4_pointwise', 'Conv2d_5'_pointwise,
      'Conv2d_6_pointwise', 'Conv2d_7_pointwise', 'Conv2d_8_pointwise',
      'Conv2d_9_pointwise', 'Conv2d_10_pointwise', 'Conv2d_11_pointwise',
      'Conv2d_12_pointwise', 'Conv2d_13_pointwise'].
    conv_defs: A list of ConvDef namedtuples specifying the net architecture.
    min_depth: Minimum depth value (number of channels) for all convolution ops.
      Enforced when depth_multiplier < 1, and not an active constraint when
      depth_multiplier >= 1.
    depth_multiplier: Float multiplier for the depth (number of channels)
      for all convolution ops. The value must be greater than zero. Typical
      usage will be to set this value in (0, 1) to reduce the number of
      parameters or computation cost of the model.
    bn_decay: Decay parameter for batch normalization layer.
    output_stride: An integer that specifies the requested ratio of input to
      output spatial resolution. If not None, then we invoke atrous convolution
      if necessary to prevent the network from reducing the spatial resolution
      of the activation maps. Allowed values are 8 (accurate fully convolutional
      mode), 16 (fast fully convolutional mode), 32 (classification mode).
    scope: Optional variable_scope.
  Returns:
    tensor_out: output tensor corresponding to the final_endpoint.
    end_points: a set of activations for external use, for example summaries or
                losses.
  Raises:
    ValueError: if final_endpoint is not set to one of the predefined values,
                or depth_multiplier <= 0, or the target output_stride is not
                allowed.
  """
  depth = lambda d: max(int(d * depth_multiplier), min_depth)
  end_points = {}

  # Used to find thinned depths for each layer.
  if depth_multiplier <= 0:
    raise ValueError('depth_multiplier is not greater than zero.')

  if output_stride is not None and output_stride not in [8, 16, 32]:
    raise ValueError('Only allowed output_stride values are 8, 16, 32.')

  with tf.variable_scope(scope, 'MobilenetV1', [inputs]):
    with slim.arg_scope([slim.conv2d, slim.separable_conv2d], padding='SAME'):
      # The current_stride variable keeps track of the output stride of the
      # activations, i.e., the running product of convolution strides up to the
      # current network layer. This allows us to invoke atrous convolution
      # whenever applying the next convolution would result in the activations
      # having output stride larger than the target output_stride.
      current_stride = 1

      # The atrous convolution rate parameter.
      rate = 1

      net = inputs
      for i, conv_def in enumerate(conv_defs):
        end_point_base = 'Conv2d_%d' % i

        if output_stride is not None and current_stride == output_stride:
          # If we have reached the target output_stride, then we need to employ
          # atrous convolution with stride=1 and multiply the atrous rate by the
          # current unit's stride for use in subsequent layers.
          layer_stride = 1
          layer_rate = rate
          rate *= conv_def.stride
        else:
          layer_stride = conv_def.stride
          layer_rate = 1
          current_stride *= conv_def.stride

        if isinstance(conv_def, Conv):
          end_point = end_point_base
          net = slim.conv2d(net, depth(conv_def.depth), conv_def.kernel,
                            stride=conv_def.stride,
                            normalizer_fn=slim.batch_norm,
                            normalizer_params={'decay': bn_decay},
                            scope=end_point)
          end_points[end_point] = net
          if end_point == final_endpoint:
            return net, end_points

        elif isinstance(conv_def, DepthSepConv):
          end_point = end_point_base + '_depthwise'

          # By passing filters=None
          # separable_conv2d produces only a depthwise convolution layer
          net = slim.separable_conv2d(net, None, conv_def.kernel,
                                      depth_multiplier=1,
                                      stride=layer_stride,
                                      rate=layer_rate,
                                      normalizer_fn=slim.batch_norm,
                                      normalizer_params={'decay': bn_decay},
                                      scope=end_point)

          end_points[end_point] = net
          if end_point == final_endpoint:
            return net, end_points

          end_point = end_point_base + '_pointwise'

          net = slim.conv2d(net, depth(conv_def.depth), [1, 1],
                            stride=1,
                            normalizer_fn=slim.batch_norm,
                            normalizer_params={'decay': bn_decay},
                            scope=end_point)

          end_points[end_point] = net
          if end_point == final_endpoint:
            return net, end_points
        else:
          raise ValueError('Unknown convolution type %s for layer %d'
                           % (conv_def.ltype, i))
  raise ValueError('Unknown final endpoint %s' % final_endpoint)


def nazorunet(inputs,
              num_classes,
              conv_defs,
              dropout_keep_prob=0.999,
              is_training=True,
              min_depth=8,
              depth_multiplier=1.0,
              prediction_fn=slim.layers.softmax,
              spatial_squeeze=True,
              reuse=None,
              scope='NazoruNet',
              global_pool=False):
  """Customized MobileNet model for Nazoru Input.
  Args:
    inputs: a tensor of shape [batch_size, height, width, channels].
    num_classes: number of predicted classes. If 0 or None, the logits layer
      is omitted and the input features to the logits layer (before dropout)
      are returned instead.
    dropout_keep_prob: the percentage of activation values that are retained.
    is_training: whether is training or not.
    min_depth: Minimum depth value (number of channels) for all convolution ops.
      Enforced when depth_multiplier < 1, and not an active constraint when
      depth_multiplier >= 1.
    depth_multiplier: Float multiplier for the depth (number of channels)
      for all convolution ops. The value must be greater than zero. Typical
      usage will be to set this value in (0, 1) to reduce the number of
      parameters or computation cost of the model.
    conv_defs: A list of ConvDef namedtuples specifying the net architecture.
    prediction_fn: a function to get predictions out of logits.
    spatial_squeeze: if True, logits is of shape is [B, C], if false logits is
        of shape [B, 1, 1, C], where B is batch_size and C is number of classes.
    reuse: whether or not the network and its variables should be reused. To be
      able to reuse 'scope' must be given.
    scope: Optional variable_scope.
    global_pool: Optional boolean flag to control the avgpooling before the
      logits layer. If false or unset, pooling is done with a fixed window
      that reduces default-sized inputs to 1x1, while larger inputs lead to
      larger outputs. If true, any input size is pooled down to 1x1.
  Returns:
    net: a 2D Tensor with the logits (pre-softmax activations) if num_classes
      is a non-zero integer, or the non-dropped-out input to the logits layer
      if num_classes is 0 or None.
    end_points: a dictionary from components of the network to the corresponding
      activation.
  Raises:
    ValueError: Input rank is invalid.
  """
  input_shape = inputs.get_shape().as_list()
  if len(input_shape) != 4:
    raise ValueError('Invalid input tensor rank, expected 4, was: %d' %
                     len(input_shape))

  with tf.variable_scope(scope, 'NazoruNet', [inputs], reuse=reuse) as scope:
    with slim.arg_scope([slim.batch_norm, slim.dropout],
                        is_training=is_training):
      final_endpoint = 'Conv2d_%i_pointwise' % (len(conv_defs) - 1)
      net, end_points = mobilenet_v1_base(inputs, scope=scope,
                                          min_depth=min_depth,
                                          depth_multiplier=depth_multiplier,
                                          conv_defs=conv_defs,
                                          final_endpoint=final_endpoint)
      with tf.variable_scope('Logits'):
        if global_pool:
          # Global average pooling.
          net = tf.reduce_mean(net, [1, 2], keep_dims=True, name='global_pool')
          end_points['global_pool'] = net
        else:
          # Pooling with a fixed kernel size.
          kernel_size = _reduced_kernel_size_for_small_input(net, [7, 7])
          net = slim.avg_pool2d(net, kernel_size, padding='VALID',
                                scope='AvgPool_1a')
          end_points['AvgPool_1a'] = net
        if not num_classes:
          return net, end_points
        # 1 x 1 x 1024
        net = slim.dropout(net, keep_prob=dropout_keep_prob, scope='Dropout_1b')
        logits = slim.conv2d(net, num_classes, [1, 1], activation_fn=None,
                             normalizer_fn=None, scope='Conv2d_1c_1x1')
        if spatial_squeeze:
          logits = tf.squeeze(logits, [1, 2], name='SpatialSqueeze')
      end_points['Logits'] = logits
      if prediction_fn:
        end_points['Predictions'] = prediction_fn(logits, scope='Predictions')
  return logits, end_points


def _reduced_kernel_size_for_small_input(input_tensor, kernel_size):
  """Define kernel size which is automatically reduced for small input.
  If the shape of the input images is unknown at graph construction time this
  function assumes that the input images are large enough.
  Args:
    input_tensor: input tensor of size [batch_size, height, width, channels].
    kernel_size: desired kernel size of length 2: [kernel_height, kernel_width]
  Returns:
    a tensor with the kernel size.
  """
  shape = input_tensor.get_shape().as_list()
  if shape[1] is None or shape[2] is None:
    kernel_size_out = kernel_size
  else:
    kernel_size_out = [min(shape[1], kernel_size[0]),
                       min(shape[2], kernel_size[1])]
  return kernel_size_out
